Honey-Pi/honeypi-pcb/PCB_V2.x/Schaltplan-27-9-2020.pdf

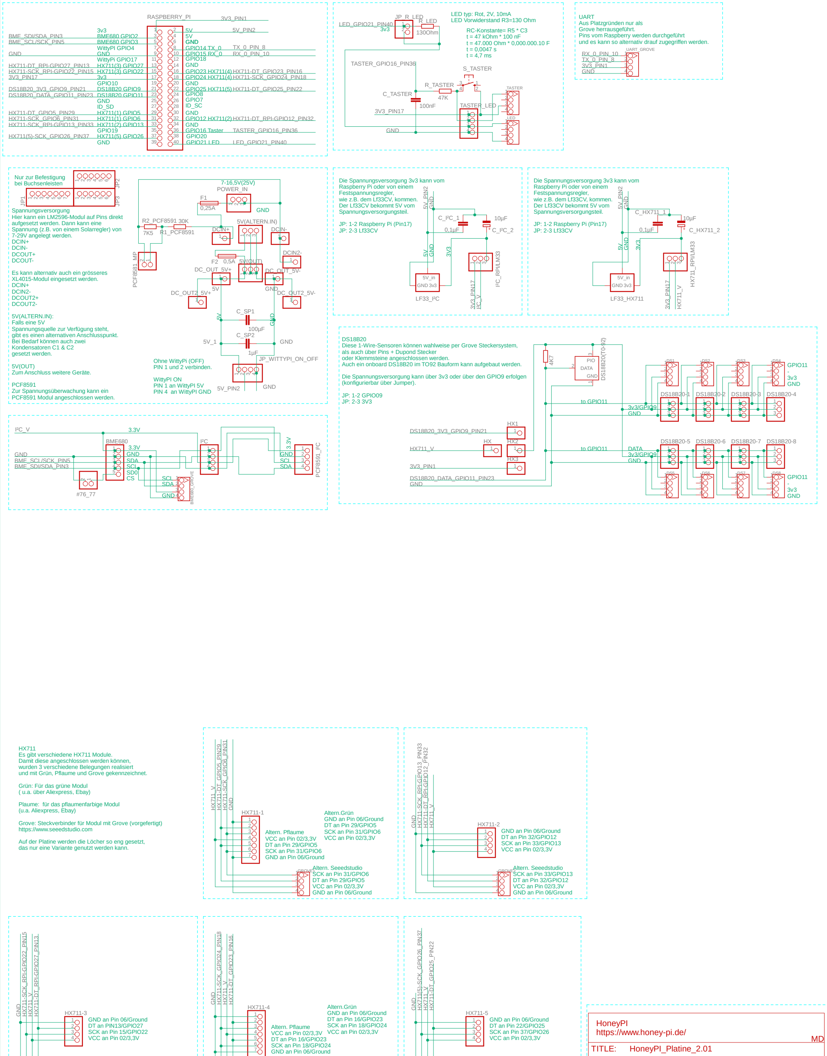
[picture p17: figure]
130Ohm; GND; RASPBERRY_PI; 4 TASTER_LED; R_LED; 1 DCIN+; 1 DCIN- 1 DC_OUT_5V+; 1 DC_OUT_5V- ¹; 3 POWER_IN; PIO; DATA 2; DS¹⁸B²⁰⁽T0⁻92⁾; 5V(OUT); R2_PCF8591; R1_PCF8591; LED; 4TASTER; C_TASTER; R_TASTER; 4GROVE1; 4GROVE2; SDA; 4 BME⁶⁸⁰_GROVE; 4UART_GROVE; 4 PCF8591_I²C; 3 I²C_RPI/LM33; C_I²C_1; 1 DC_OUT2_5V+; 1 DCIN2- 1 DC_OUT2_5V-; 4 2 S_TASTER; 1 PCF8581_MP; I²C; 5 BME680; 3 HX711_RPI/LM33; JP_WITTYPI_ON_OFF; 5V(ALTERN.IN); 5V_in GND 3v3; LF33_I²C; C_I²C_2; JP_R_LED; BME_SCL/SCK_PIN5; HX⁷¹¹_V; HX⁷¹¹_V HX⁷¹¹_V; DS18B20_3V3_GPIO9_PIN21; LED_GPIO21_PIN40; TASTER_GPIO16_PIN36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

1
2
3

4GROVE3

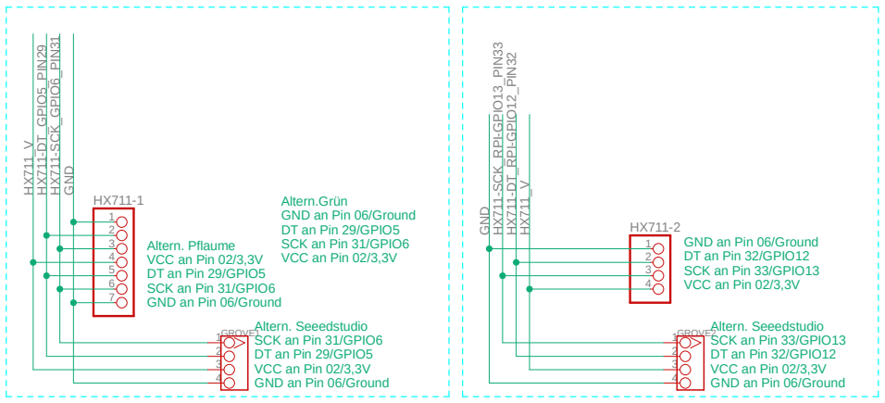
[picture p18: figure]

1
2
3
4GROVE4 | 1
2
3

4GROVE5

HX711-DT_GPIO5_PIN29 | HX⁷¹¹⁻DT_GPIO⁵_PIN²⁹
HX711-DT_RPI-GPIO12_PIN32 | HX⁷¹¹⁻DT_RPI-GPIO¹²_PIN³²

# TASTER_GPIO16_PIN36 HX⁷¹¹⁻SCK_RPI-GPIO¹³_PIN³³

HX711-DT_RPI-GPIO27_PIN13 HX⁷¹¹⁻SCK_RPI-GPIO²²_PIN¹⁵ | HX⁷¹¹⁻DT_RPI-GPIO²⁷_PIN¹³
HX711-SCK_RPI-GPIO22_PIN15 | HX711-DT_GPIO23_PIN16 HX⁷¹¹⁻DT_GPIO²³_PIN¹⁶

# HX711-SCK_GPIO24_PIN18 HX⁷¹¹⁻SCK_GPIO²⁴_PIN¹⁸

HX711-SCK_GPIO6_PIN31 | HX⁷¹¹⁻SCK_GPIO⁶_PIN³¹
HX711-DT_GPIO25_PIN22 | HX⁷¹¹⁽⁵⁾⁻SCK_GPIO²⁶_PIN³⁷ | HX⁷¹¹⁻DT_GPIO²⁵_PIN²²
Date: | Sheet:

## REV:

## Document Number:

27.09.2020 13:27 | 1/1

Altern. Pflaume VCC an Pin 02/3,3V DT an Pin 29/GPIO5 SCK an Pin 31/GPIO6 GND an Pin 06/Ground

Altern.Grün GND an Pin 06/Ground DT an Pin 29/GPIO5 SCK an Pin 31/GPIO6 VCC an Pin 02/3,3V

DS18B20 GPIO9 DS18B20 GPIO11 HX711(1) GPIO5

HX711(2) GPIO13 GND GND | GND GPIO16 Taster GPIO21 LED GND GND GND GND
Altern. Seeedstudio SCK an Pin 31/GPIO6 DT an Pin 29/GPIO5 VCC an Pin 02/3,3V GND an Pin 06/Ground | GND an Pin 06/Ground DT an Pin 32/GPIO12 SCK an Pin 33/GPIO13 VCC an Pin 02/3,3V

Altern. Seeedstudio SCK an Pin 33/GPIO13 DT an Pin 32/GPIO12 VCC an Pin 02/3,3V GND an Pin 06/Ground GND an Pin 06/Ground DT an PIN13/GPIO27 SCK an Pin 15/GPIO22 VCC an Pin 02/3,3V

Altern. Seeedstudio SCK an Pin 15/GPIO22 DT an PIN13/GPIO27 VCC an Pin 02/3,3V GND an Pin 06/Ground | Altern. Pflaume VCC an Pin 02/3,3V DT an Pin 16/GPIO23 SCK an Pin 18/GPIO24 GND an Pin 06/GroundAltern.Grün GND an Pin 06/Ground DT an Pin 16/GPIO23 SCK an Pin 18/GPIO24 VCC an Pin 02/3,3V
Altern. Seeedstudio SCK an Pin 18/GPIO24 DT an Pin 16/GPIO23 VCC an Pin 02/3,3V GND an Pin 06/Ground | GND an Pin 06/Ground DT an Pin 22/GPIO25 SCK an Pin 37/GPIO26 VCC an Pin 02/3,3V

Altern. Seeedstudio SCK an Pin 37/GPIO26 DT an Pin 22/GPIO25 VCC an Pin 02/3,3V GND an Pin 06/Ground

HX711 Es gibt verschiedene HX711 Module.

und mit Grün, Pflaume und Grove gekennzeichnet.

Grove: Steckverbinder für Modul mit Grove (vorgefertigt)

Auf der Platine werden die Löcher so eng gesetzt,
das nur eine Variante genutzt werden kann.

DS18B20 Diese 1-Wire-Sensoren können wahlweise per Grove Steckersystem,

Auch ein onboard DS18B20 im TO92 Bauform kann aufgebaut werden.

Die Spannungsversorgung kann über 3v3 oder über den GPIO9 erfolgen (konfigurierbar über Jumper). JP: 1-2 GPIO09

und es kann so alternativ drauf zugegriffen werden.

Spannungsversorgung Hier kann ein LM2596-Modul auf Pins direkt aufgesetzt werden. Dann kann eine

Spannung (z.B. von einem Solarregler) von 7-29V angelegt werden. DCIN+ DCIN- DCOUT+ DCOUT- Es kann alternativ auch ein grösseres

XL4015-Modul eingesetzt werden. DCIN+ DCIN2- DCOUT2+ DCOUT2- 5V(ALTERN.IN): Falls eine 5V

gibt es einen alternativen Anschlusspunkt. Bei Bedarf können auch zwei Kondensatoren C1 & C2

5V(OUT) Zum Anschluss weitere Geräte. PCF8591 Zur Spannungsüberwachung kann ein

wie z.B. dem Lf33CV, kommen. Der Lf33CV bekommt 5V vom

JP: 1-2 Raspberry Pi (Pin17) JP: 2-3 Lf33CV wie z.B. dem Lf33CV, kommen. Der Lf33CV bekommt 5V vom

JP: 1-2 Raspberry Pi (Pin17) JP: 2-3 Lf33CV

A

B

C

D

E

1 | 2 | 3 | 4 | 5 | 6 | 7 | 8

A

B

C

D

E

1 | 2 | 3 | 4 | 5 | 6 | 7 | 8

Ohne WittyPi (OFF) PIN 1 und 2 verbinden. WittyPI ON
