Honey-Pi/honeypi-pcb/PCB_V2.x/Schaltplan-21-8-2020.pdf

100µF

1µF

130Ohm

130Ohm | 4K⁷
5V | GND

7K5

30K

100nF

47K

0,1µF | 0,1µF
10µF | 10µF

0,25A

0,5A

1 2
3 4
5 6
7 8
9 10
11 12
13 14
15 16
17 18
19 20
21 22
23 24
25 26
27 28
29 30
31 32
33 34
35 36
37 38
39 40

RASPBERRY_PI

C_SP1

C_SP2

1
2
3

### 4 TASTER_LED

R_LED

### 1 DCIN+

### 1 DCIN- 1 DC_OUT_5V+

### 1 DC_OUT_5V- ¹

2

### 3 POWER_IN

1
2
3
4
5
6

# 7 HX711-1

PIO

GND

DATA 2 | 1 3 | DS¹⁸B²⁰⁽T0⁻92⁾

1

2

3

5V(OUT)

1
2

### 3 DS18B20-8

1
2

### 3 DS18B20-4

1
2

### 3 DS18B20-3

1
2

### 3 DS18B20-2

1
2

### 3 DS18B20-1

1
2

### 3 DS18B20-6

1
2

### 3 DS18B20-7

1
2

### 3 DS18B20-5

R2_PCF8591

R1_PCF8591

1
2
3

4DS8 1
2
3

4DS7 1
2
3

4DS6 1
2
3

4DS5

1
2
3
4DS1 | 1
2
3
4DS2 | 1
2
3
4DS3 | 1
2
3

4DS4

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
4TASTER

1
2
3

JP_VORW

C_TASTER

R_TASTER

1
2
3
4SEEED1 | 1
2
3

4SEEED2

1
2
3

4SEEED3

1
2
3
4
5
6

# 7 HX711-4

1
2
3
4SEEED4 | 1
2
3

4SEEED5

1
2
3

### 4 BME⁶⁸⁰_GROVE

1
2
3

4UART_GROVE

1
2
3

### 4 PCF8591_I²C

1

2

### 3 I²C_RPI/LM33

C_I²C_1

### 1 DC_OUT2_5V+

### 1 DCIN2- 1 DC_OUT2_5V-

3 1

4 2 S_TASTER

2

### 1 PCF8581_MP

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
### 5 BME680

1
2
3

### 4 HX711-3

1
2
3

### 4 HX711-2

1
2
3

### 4 HX711-5

1

2

# 3 HX711_RPI/LM33

C_HX711_1

1

2

3

4

JP_WITTYPI_ON_OFF

1

2

3

5V(ALTERN.IN)

### 1 HX

2

1

#76_77

5V_in GND 3v3

LM33_I²C

5V_in GND 3v3

LM33_HX711

C_I²C_2 | C_HX711_2 F1 F2
1

2

3

4

5

6

### 7 JP1

1

2

3

4

5

### 6 JP2

1

2

3

4

5

### 6 JP3

### 1 HX1

### 1 HX2

### 1 HX3

# HX711-DT_GPIO5_PIN29 HX⁷¹¹⁻DT_GPIO⁵_PIN²⁹

BME_SCL/SCK_PIN5

BME_SCL/SCK_PIN5 | HX⁷¹¹_V | HX⁷¹¹_V | HX⁷¹¹_V HX⁷¹¹_V | HX⁷¹¹_V | HX⁷¹¹_V

HX711_V

# HX711-DT_RPI-GPIO12_PIN32 HX⁷¹¹⁻DT_RPI-GPIO¹²_PIN³²

DS18B20_3V3_GPIO9_PIN21

DS18B20_3V3_GPIO9_PIN21

LED_GPIO21_PIN40

LED_GPIO21_PIN40

TASTER_GPIO16_PIN36

# TASTER_GPIO16_PIN36 HX⁷¹¹⁻SCK_RPI-GPIO¹³_PIN³³

HX711-SCK_RPI-GPIO13_PIN33

HX711-DT_RPI-GPIO27_PIN13 HX⁷¹¹⁻SCK_RPI-GPIO²²_PIN¹⁵ | HX⁷¹¹⁻DT_RPI-GPIO²⁷_PIN¹³
HX711-SCK_RPI-GPIO22_PIN15 | HX711-DT_GPIO23_PIN16 HX⁷¹¹⁻DT_GPIO²³_PIN¹⁶

# HX711-SCK_GPIO24_PIN18 HX⁷¹¹⁻SCK_GPIO²⁴_PIN¹⁸

HX711-SCK_GPIO6_PIN31 | HX⁷¹¹⁻SCK_GPIO⁶_PIN³¹
HX711-DT_GPIO25_PIN22 | HX⁷¹¹⁽⁵⁾⁻SCK_GPIO²⁶_PIN³⁷ | HX⁷¹¹⁻DT_GPIO²⁵_PIN²²

HX711(5)-SCK_GPIO26_PIN37

TX_0_PIN_8

TX_0_PIN_8

RX_0_PIN_10

RX_0_PIN_10

BME_SDI/SDA_PIN3

BME_SDI/SDA_PIN3

3V3_PIN17

3V3_PIN17 | 3V³_PIN¹⁷ | 3V³_PIN¹⁷

3V3_PIN1

3V3_PIN1

3V3_PIN1

I²C_V | I²C_V ⁵V_PIN²
5V_PIN2 | 5V_PIN²

5V_PIN2

DS18B20_DATA_GPIO11_PIN23

DS18B20_DATA_GPIO11_PIN23

5V_1 | GND GND

GND

GND GND

GND | GND GND | GND GND | GND GND | GND | GND

## HoneyPI

https://www.honey-pi.de/ | MD
Date: | Sheet:

## REV:

## TITLE:

## Document Number:

21.08.2020 11:47 | 1/1

## HoneyPI_Platine_2.01

+

+

3v3

5V

3v3/GPIO9 GND | DATA
SCL | GND

SDA

SD0 CS

3v3 5V | GND GND

7-16,5V(25V)

Altern. Pflaume VCC an Pin 02/3,3V DT an Pin 29/GPIO5 SCK an Pin 31/GPIO6 GND an Pin 06/Ground

GPIO18

Altern.Grün GND an Pin 06/Ground DT an Pin 29/GPIO5 SCK an Pin 31/GPIO6 VCC an Pin 02/3,3V

BME680 GPIO2 BME680 GPIO3 WittyPI GPIO4

WittyPi GPIO17 GND

DS18B20 GPIO9 DS18B20 GPIO11 HX711(1) GPIO5

HX711(1) GPIO6

HX711(2) GPIO13 GND GND | GND GPIO16 Taster GPIO21 LED GND GND GND GND 5VGPIO12 HX711(2)

3v3/GPIO9 GND

to GPIO11 | GPIO11

-3v3 GND

GPIO11
-3v3 GND

to GPIO11

GPIO23 HX711(4)
GPIO24 HX711(4)

GPIO25 HX711(5)

HX711(5) GPIO26 | GND GPIO15 RX_0 GPIO14 TX_0

HX711(3) GPIO27
HX711(3) GPIO22
Altern. Seeedstudio SCK an Pin 31/GPIO6 DT an Pin 29/GPIO5 VCC an Pin 02/3,3V GND an Pin 06/Ground | GND an Pin 06/Ground DT an Pin 32/GPIO12 SCK an Pin 33/GPIO13 VCC an Pin 02/3,3V

Altern. Seeedstudio SCK an Pin 33/GPIO13 DT an Pin 32/GPIO12 VCC an Pin 02/3,3V GND an Pin 06/Ground GND an Pin 06/Ground DT an PIN13/GPIO27 SCK an Pin 15/GPIO22 VCC an Pin 02/3,3V

Altern. Seeedstudio SCK an Pin 15/GPIO22 DT an PIN13/GPIO27 VCC an Pin 02/3,3V GND an Pin 06/Ground | Altern. Pflaume VCC an Pin 02/3,3V DT an Pin 16/GPIO23 SCK an Pin 18/GPIO24 GND an Pin 06/GroundAltern.Grün GND an Pin 06/Ground DT an Pin 16/GPIO23 SCK an Pin 18/GPIO24 VCC an Pin 02/3,3V
Altern. Seeedstudio SCK an Pin 18/GPIO24 DT an Pin 16/GPIO23 VCC an Pin 02/3,3V GND an Pin 06/Ground | GND an Pin 06/Ground DT an Pin 22/GPIO25 SCK an Pin 37/GPIO26 VCC an Pin 02/3,3V

Altern. Seeedstudio SCK an Pin 37/GPIO26 DT an Pin 22/GPIO25 VCC an Pin 02/3,3V GND an Pin 06/Ground

GND

SDA

# SCL³.3V GPIO8 GPIO7

ID_SC GPIO20

# ID_SD GPIO10 GPIO19

HX711 Es gibt verschiedene HX711 Module.

Damit diese angeschlossen werden können, wurden 3 verschiedene Belegungen realisiert
und mit Grün, Pflaume und SEEED gekennzeichnet.

Grün: Für das grüne Modul
( u.a. über Aliexpress, Ebay)

Plaume: für das pflaumenfarbige Modul
(u.a. Aliexpress, Ebay)

Seeed: Modul mit Grove vorgefertigt https://www.seeedstudio.com

Auf der Platine werden die Löcher so eng gesetzt, das nur eine Variante genutzt werden kann.

DS18B20 Diese 1-Wire-Sensoren können wahlweise per Grove Steckersystem,

als auch über Pins + Dupond Stecker
oder Klemmsteine angeschlossen werden.
Auch ein onboard DS18B20 im TO92 Bauform kann aufgebaut werden.

Die Spannungsversorgung kann über 3v3 oder über den GPIO9 erfolgen (konfigurierbar über Jumper). JP: 1-2 GPIO09

JP: 2-3 3V3

UART Aus Platzgründen nur als

Grove herrausgeführt.
Pins vom Raspberry werden durchgeführt
und es kann so alternativ drauf zugegriffen werden.

Spannungsversorgung Hier kann ein LM2596-Modul auf Pins direkt aufgesetzt werden. Dann kann eine

Spannung (z.B. von einem Solarregler) von 7-29V angelegt werden. DCIN+ DCIN- DCOUT+ DCOUT- Es kann alternativ auch ein grösseres

XL4015-Modul eingesetzt werden. DCIN+ DCIN2- DCOUT2+ DCOUT2- 5V(ALTERN.IN): Falls eine 5V

Spannungsquelle zur Verfügung steht, gibt es einen alternativen Anschlusspunkt. Bei Bedarf können auch zwei Kondensatoren C1 & C2

gesetzt werden.

5V(OUT) Zum Anschluss weitere Geräte. PCF8591 Zur Spannungsüberwachung kann ein

PCF8591 Modul angeschlossen werden. | 5VGND | 3V³
3v3 | Die Spannungsversorgung 3v3 kann vom

Raspberry Pi oder von einem Festspannungsregler,
wie z.B. dem LM33CV, kommen. Der LM33CV bekommt 5V vom

Spannungsversorgungsteil.

JP: 1-2 Raspberry Pi (Pin17) JP: 2-3 LM33CV

RC-Konstante= R5 * C3
t = 47 kOhm * 100 nF
t = 47.000 Ohm * 0,000.000.10 F t = 0,0047 s
t = 4,7 ms

LED typ: Rot, 2V, 10mA
LED Vorwiderstand R3=130 Ohm

3.3V

3.3V | GND

SDA

SCL | 5VGND | 3V³

Die Spannungsversorgung 3v3 kann vom Raspberry Pi oder von einem Festspannungsregler,
wie z.B. dem LM33CV, kommen. Der LM33CV bekommt 5V vom

Spannungsversorgungsteil.

JP: 1-2 Raspberry Pi (Pin17) JP: 2-3 LM33CV

A

B

C

D

E

1 | 2 | 3 | 4 | 5 | 6 | 7 | 8

A

B

C

D

E

1 | 2 | 3 | 4 | 5 | 6 | 7 | 8

Ohne WittyPi (OFF) PIN 1 und 2 verbinden. WittyPI ON

PIN 1 an WittyPI 5V
PIN 4 an WittyPI GND

Nur zur Befestigung
bei Buchsenleisten
