Honey-Pi/honeypi-pcb/PCB_Sensor_Board_2.x_BME280_680_ATH10_HDC1080/Datasheets/Gehäusemaße.jpg

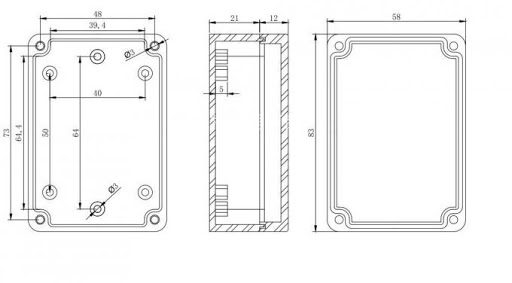
PCB_Sensor_Board_2.x_BME280_680_ATH10_HDC1080/Datasheets/Gehäusemaße.jpg
