Honey-Pi/honeypi-pcb/PCB_V3.x/Doku/D1.png

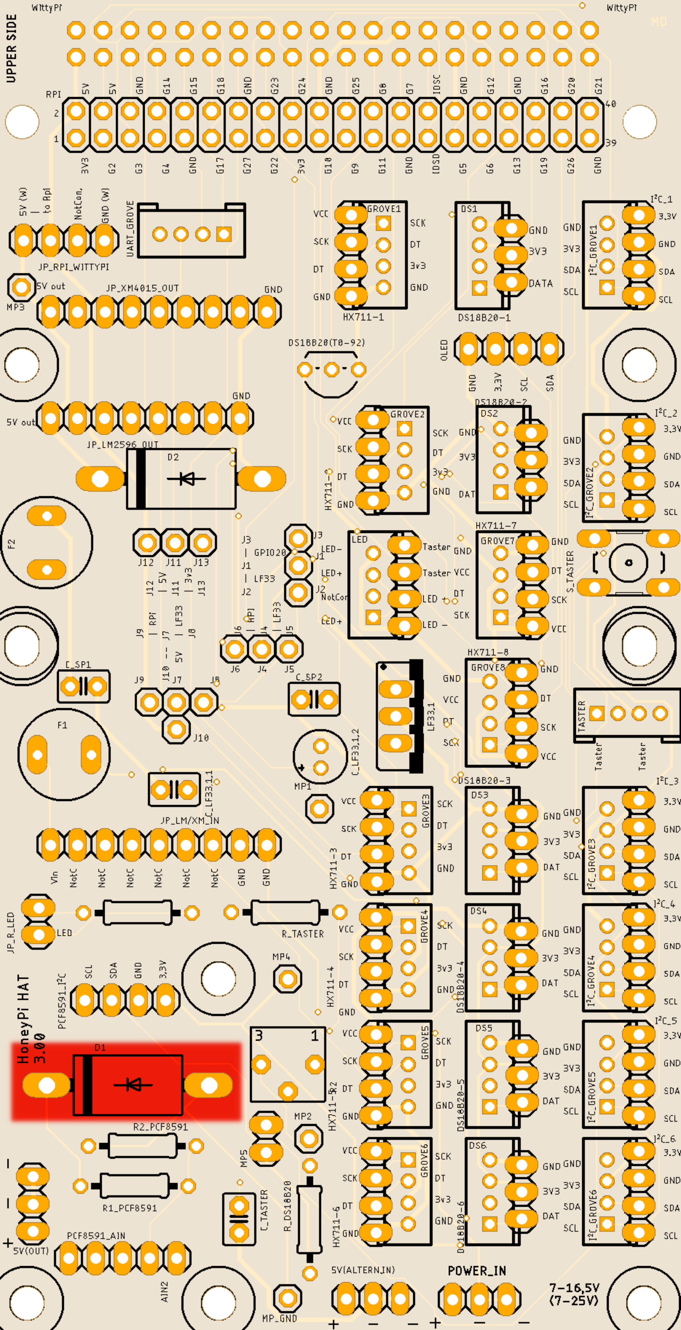
PCB_V3.x/Doku/D1.png
