Honey-Pi/honeypi-pcb/PCB_V3.x/Doku/D2.png

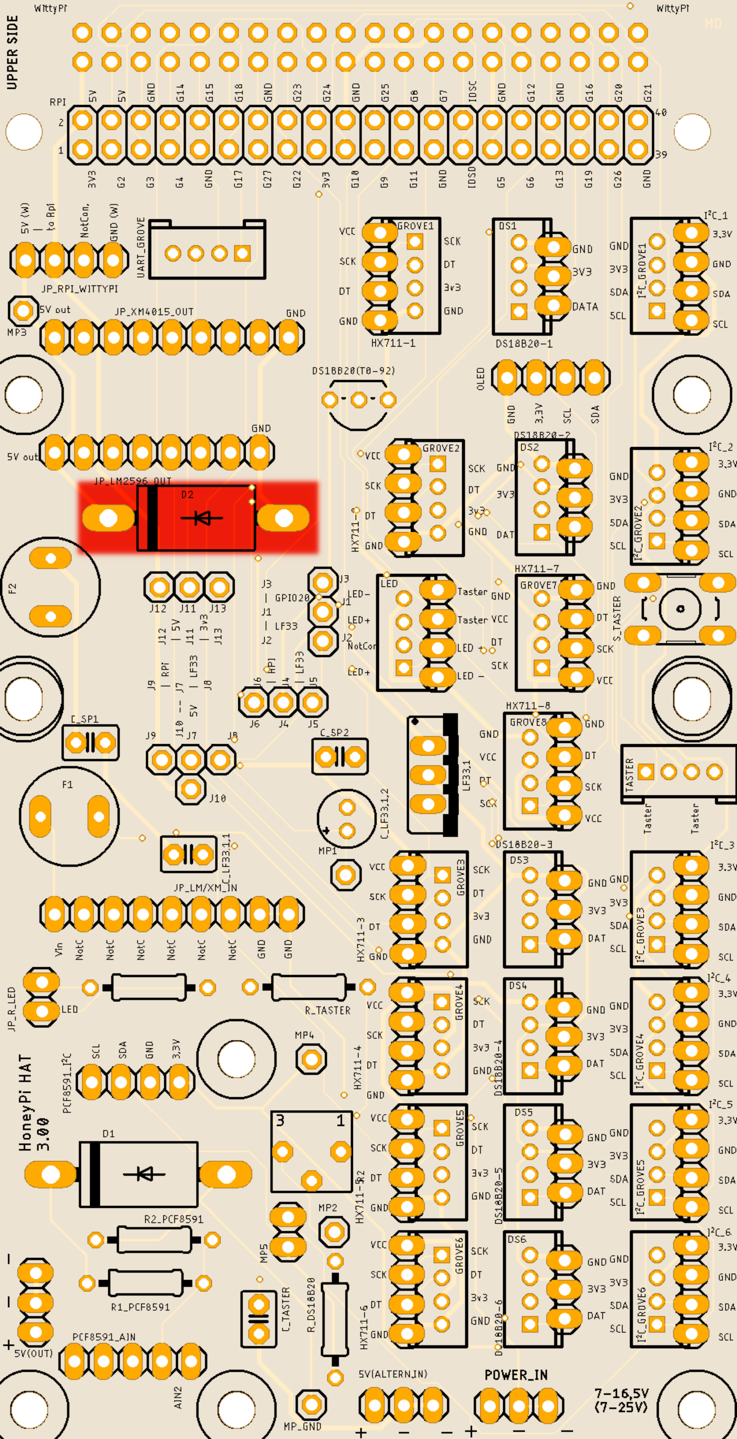
PCB_V3.x/Doku/D2.png
