Honey-Pi/honeypi-pcb/PCB_V3.x/Doku/ds18b20.png

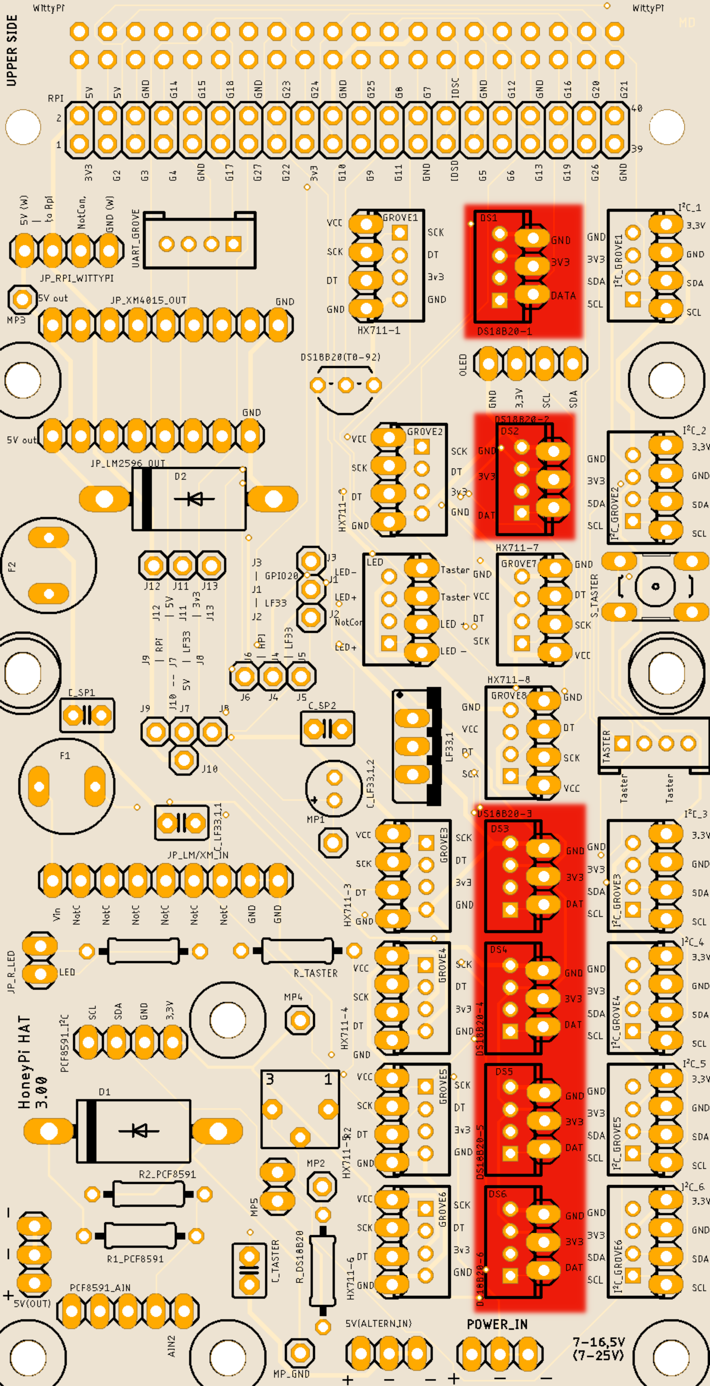
PCB_V3.x/Doku/ds18b20.png
