Honey-Pi/honeypi-pcb/PCB_V3.x/Doku/DS18B20_kompl.png

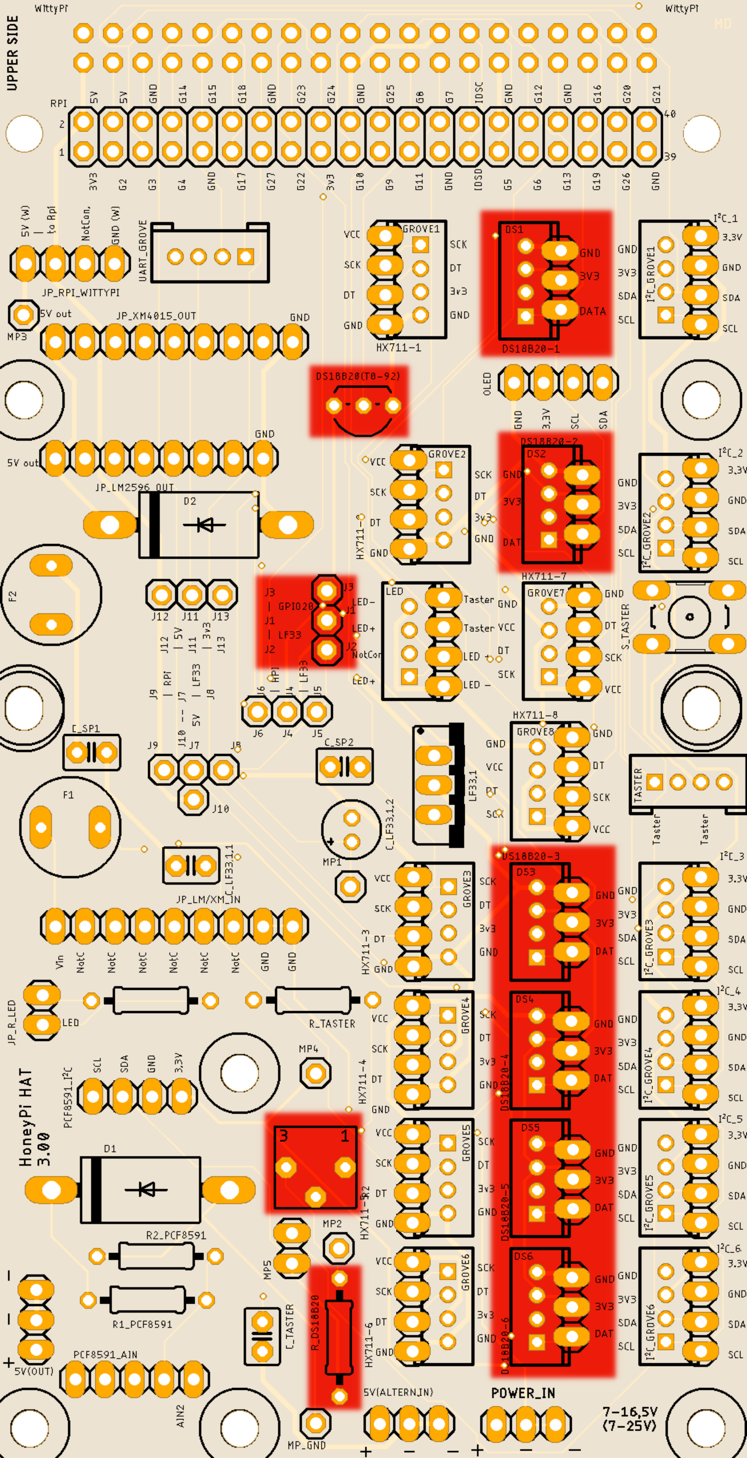
PCB_V3.x/Doku/DS18B20_kompl.png
