Honey-Pi/honeypi-pcb/PCB_V3.x/Doku/DS18B20_Potent_R.png

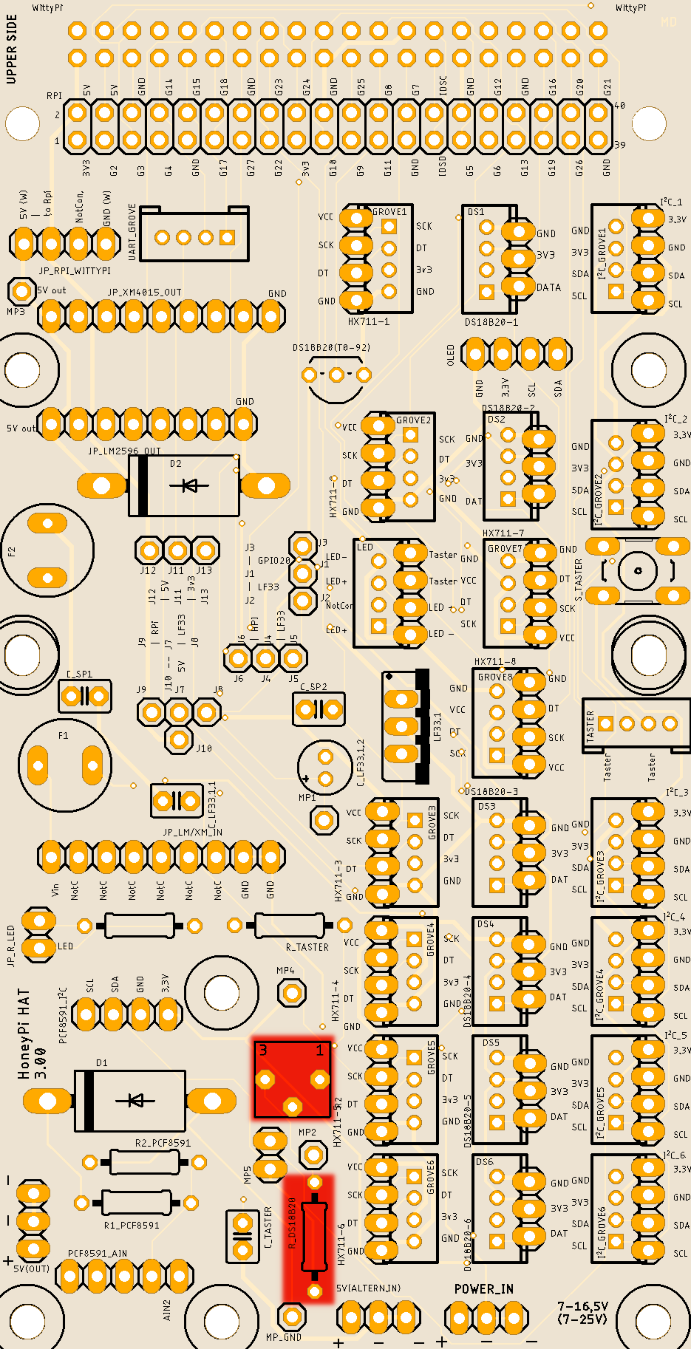
PCB_V3.x/Doku/DS18B20_Potent_R.png
