Honey-Pi/honeypi-pcb/PCB_V3.x/Doku/Ds18B20OnBoard.png

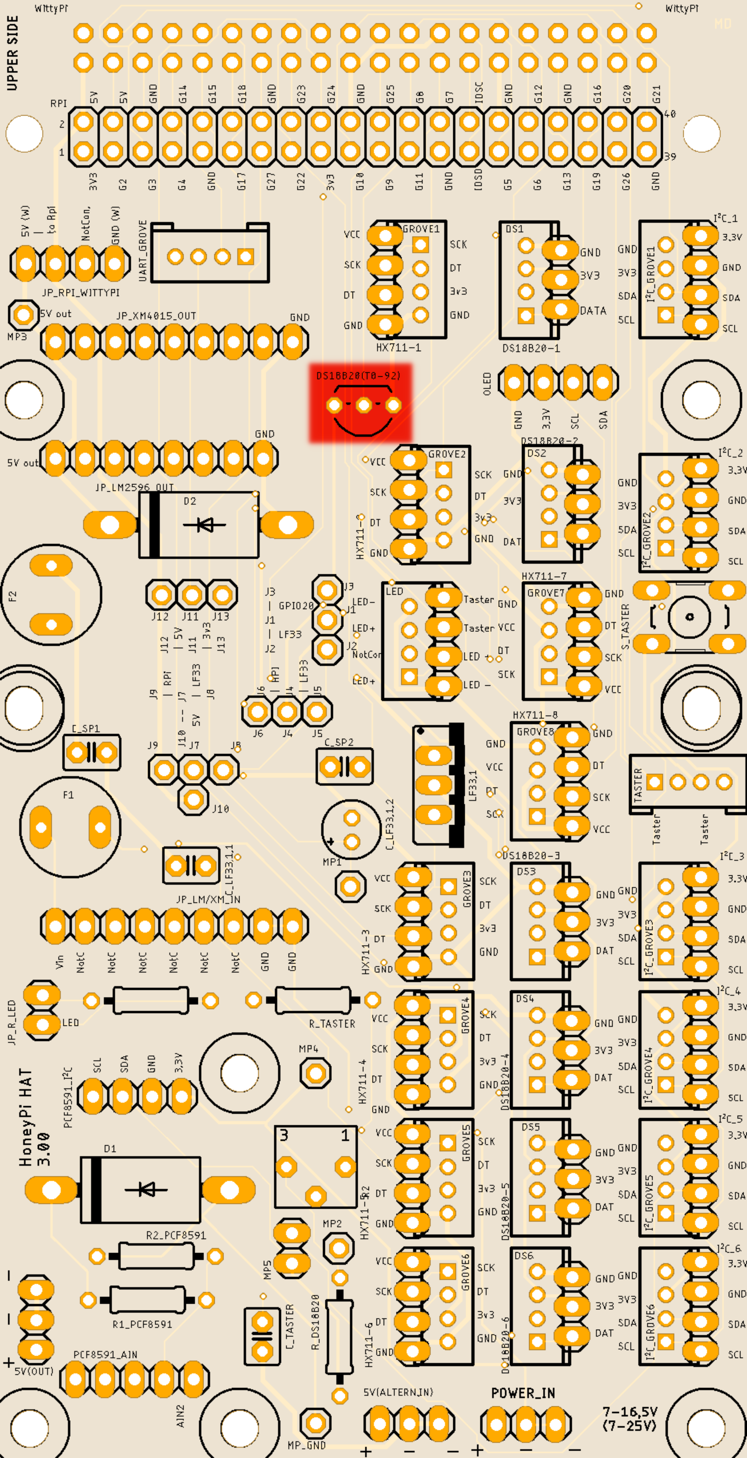
PCB_V3.x/Doku/Ds18B20OnBoard.png
