Honey-Pi/honeypi-pcb/PCB_V3.x/Doku/F1.png

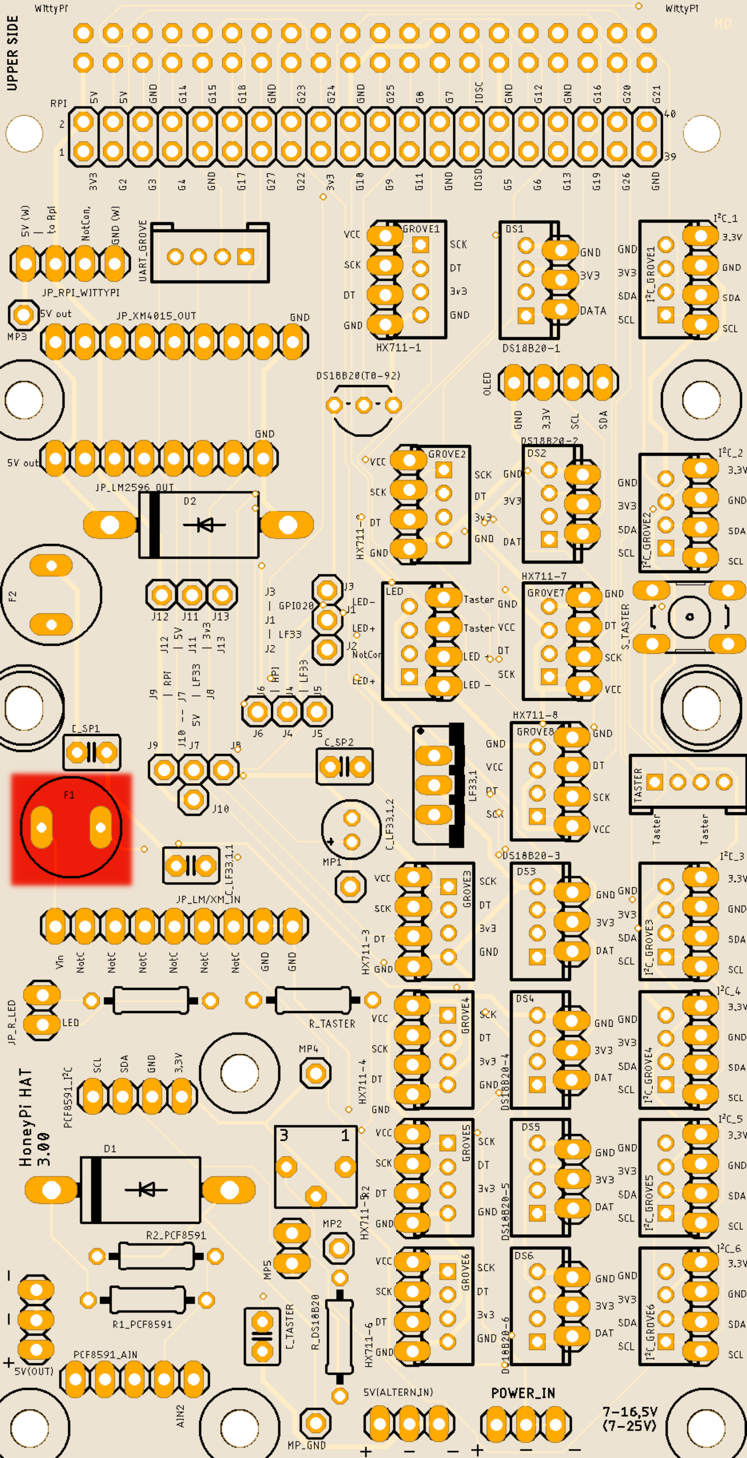
PCB_V3.x/Doku/F1.png
