Honey-Pi/honeypi-pcb/PCB_V3.x/Doku/hx711.png

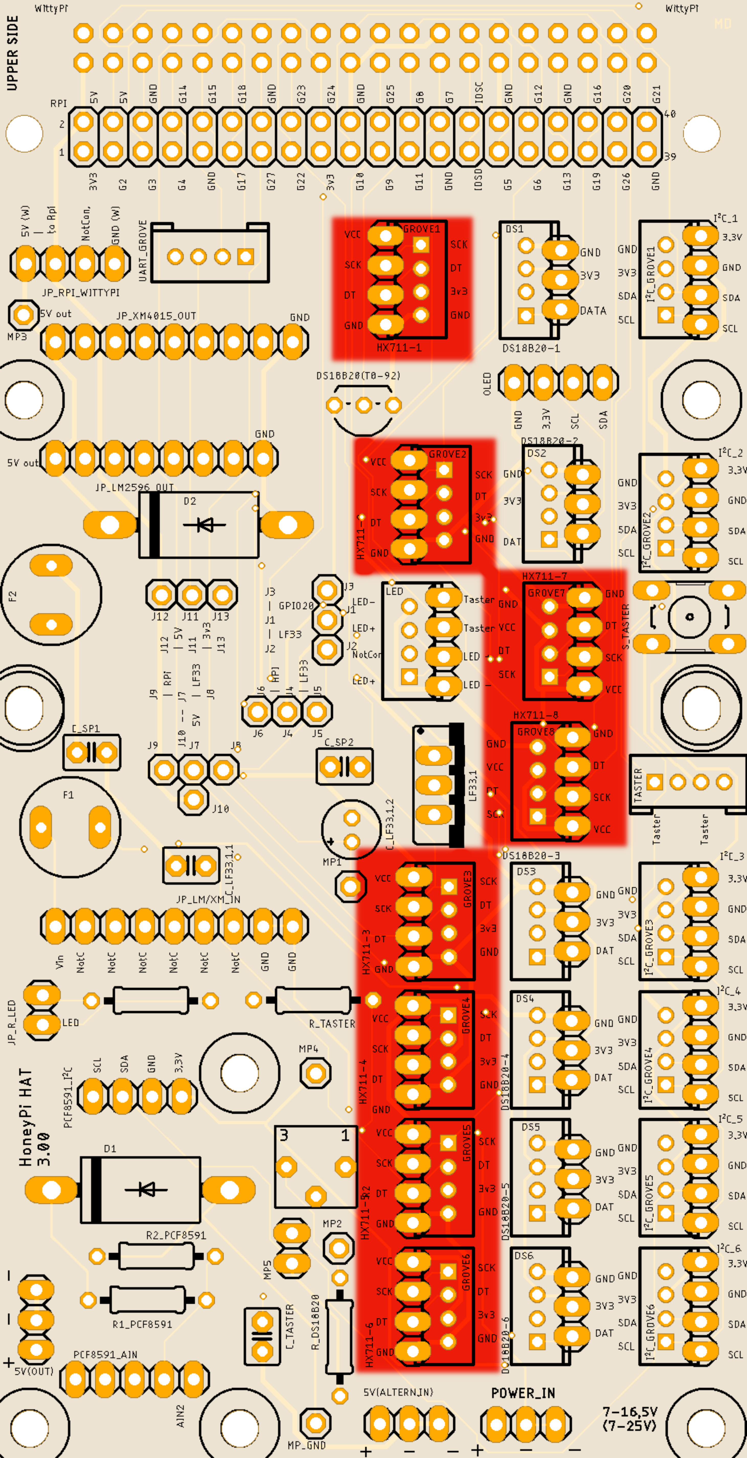
PCB_V3.x/Doku/hx711.png
