Honey-Pi/honeypi-pcb/PCB_V3.x/Doku/I2c.png

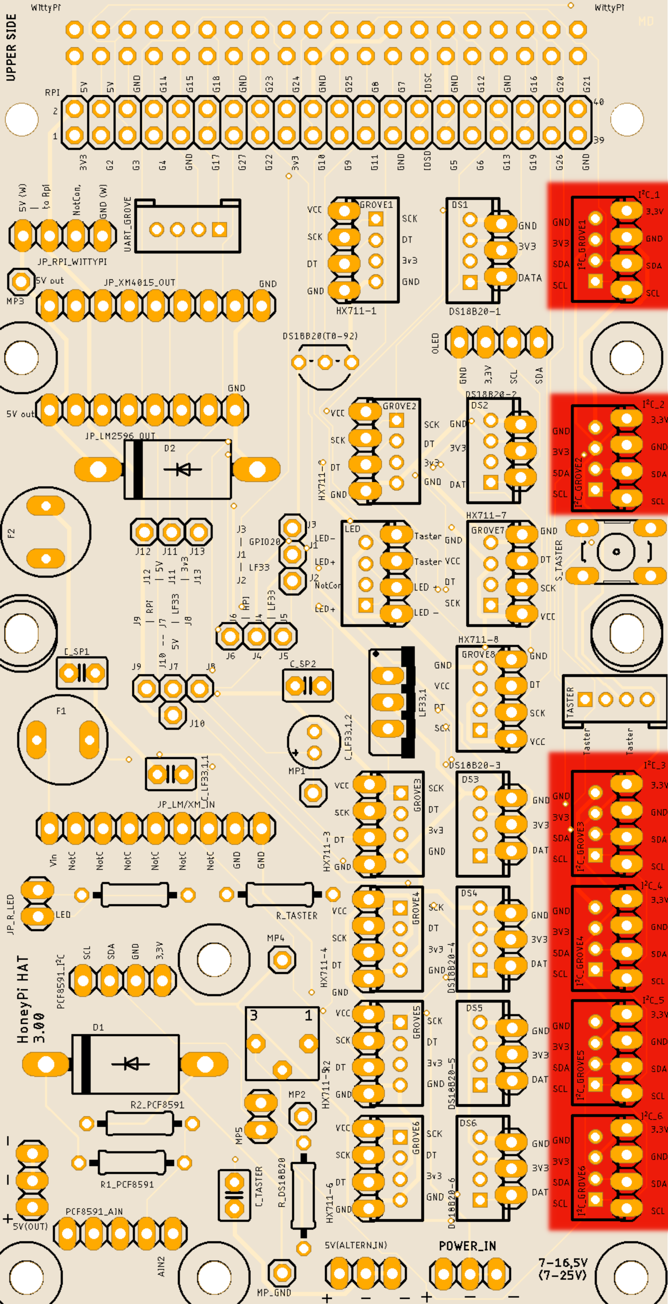
PCB_V3.x/Doku/I2c.png
