Honey-Pi/honeypi-pcb/PCB_V3.x/Doku/LF33.png

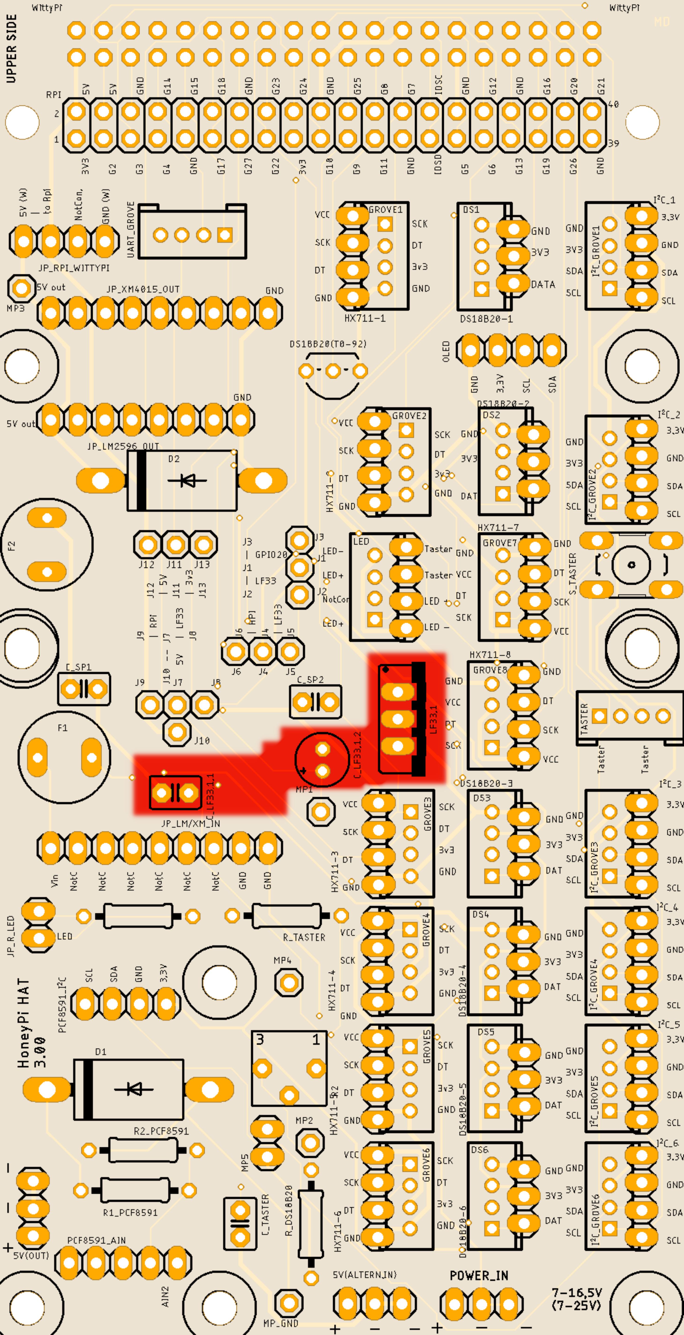
PCB_V3.x/Doku/LF33.png
