Honey-Pi/honeypi-pcb/PCB_V3.x/Doku/LM2596.png

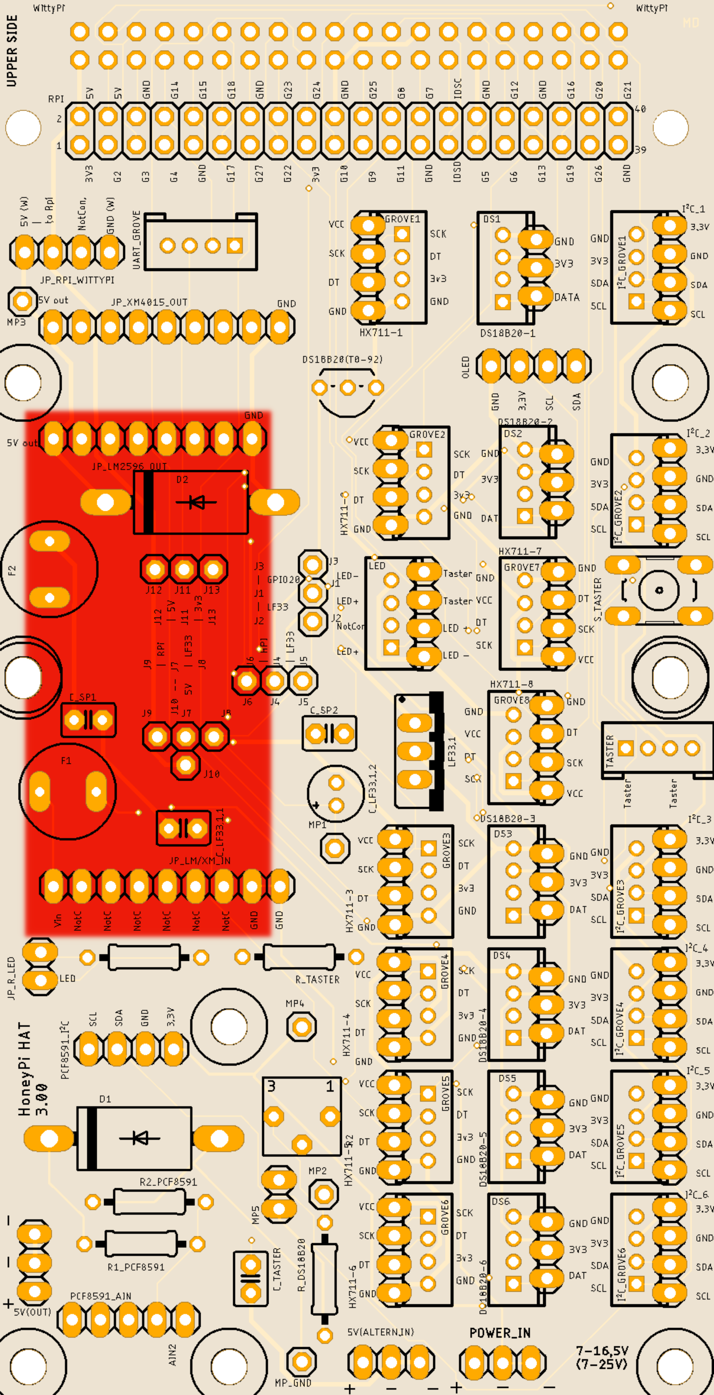
PCB_V3.x/Doku/LM2596.png
