Honey-Pi/honeypi-pcb/PCB_V3.x/Doku/pcf.png

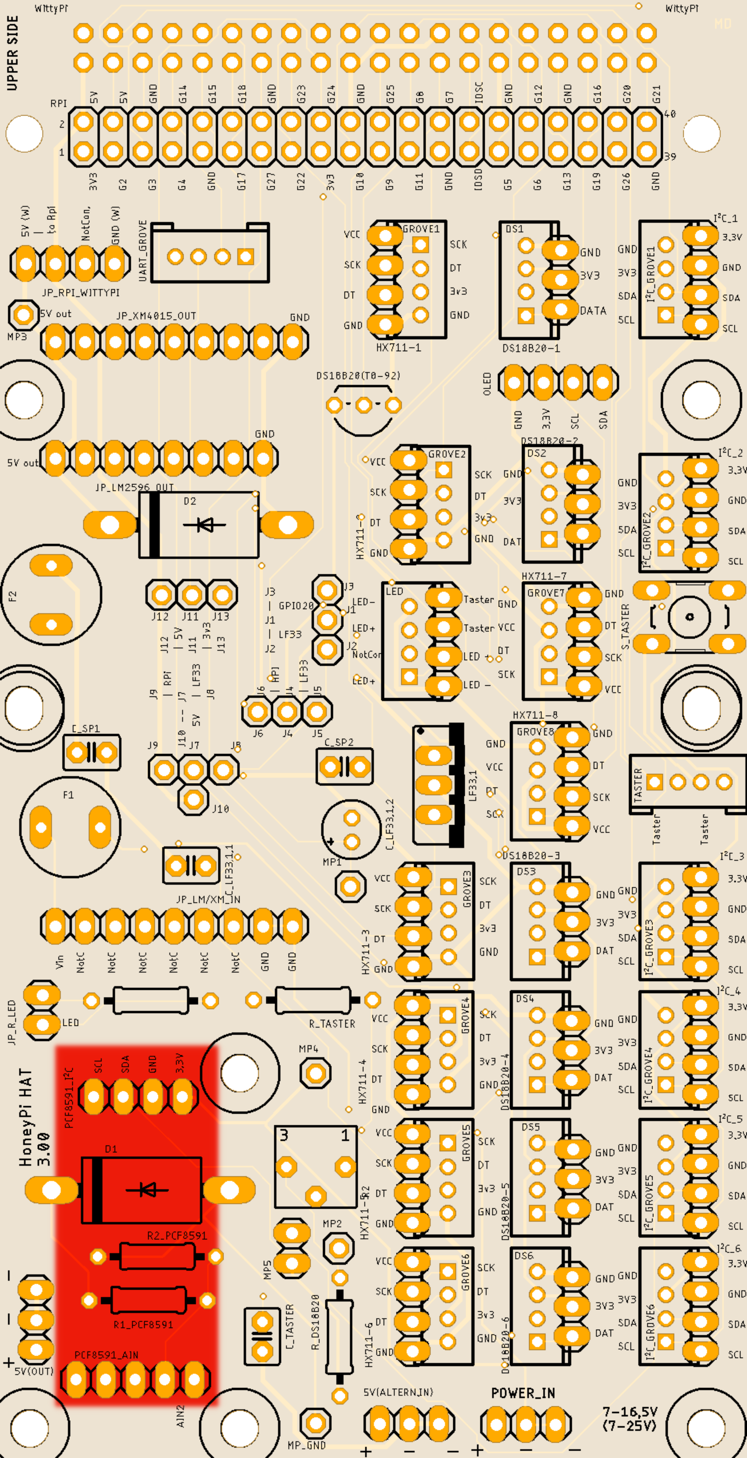
PCB_V3.x/Doku/pcf.png
