Honey-Pi/honeypi-pcb/PCB_V3.x/Doku/Power_Alternativ_ohne WittyPi_kompl.png

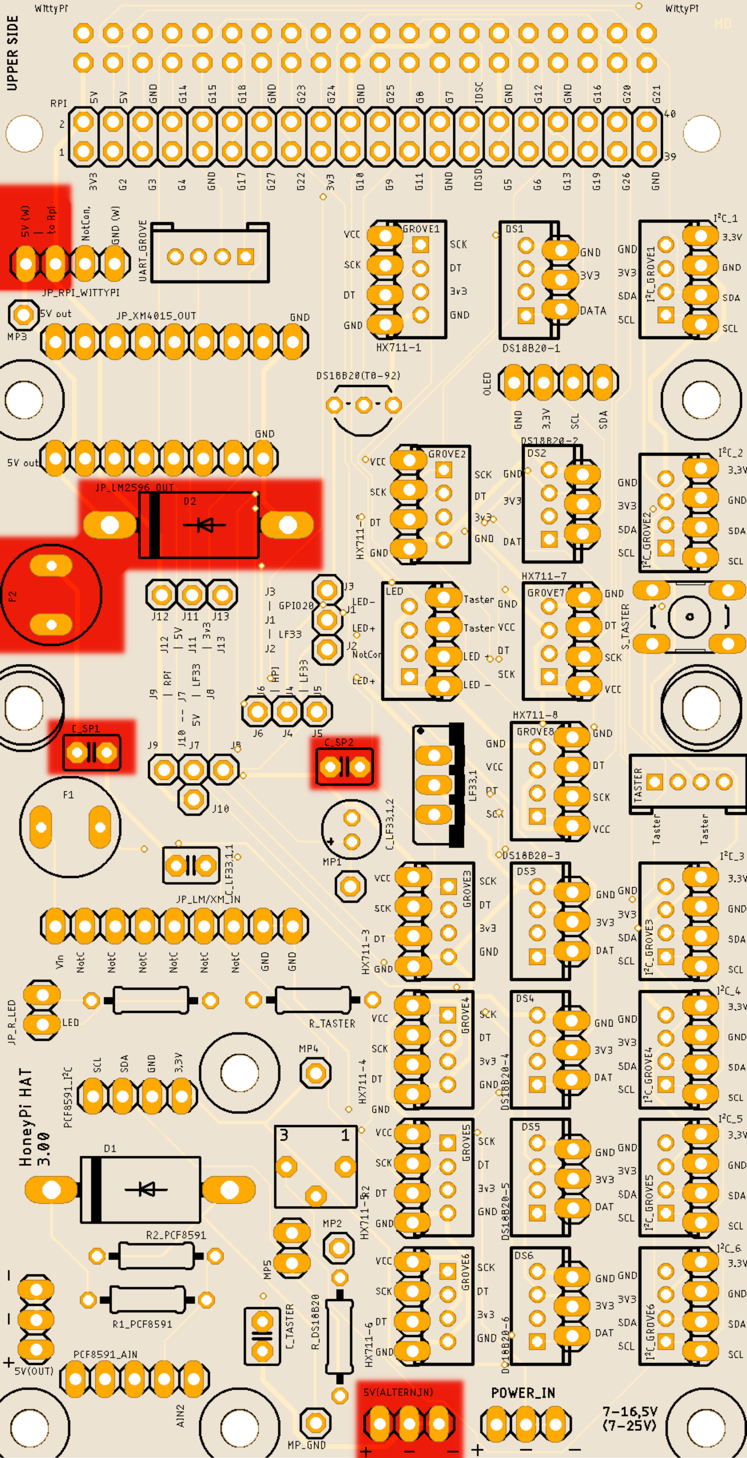
PCB_V3.x/Doku/Power_Alternativ_ohne WittyPi_kompl.png
