Honey-Pi/honeypi-pcb/PCB_V3.x/Doku/PowerAlternativ.png

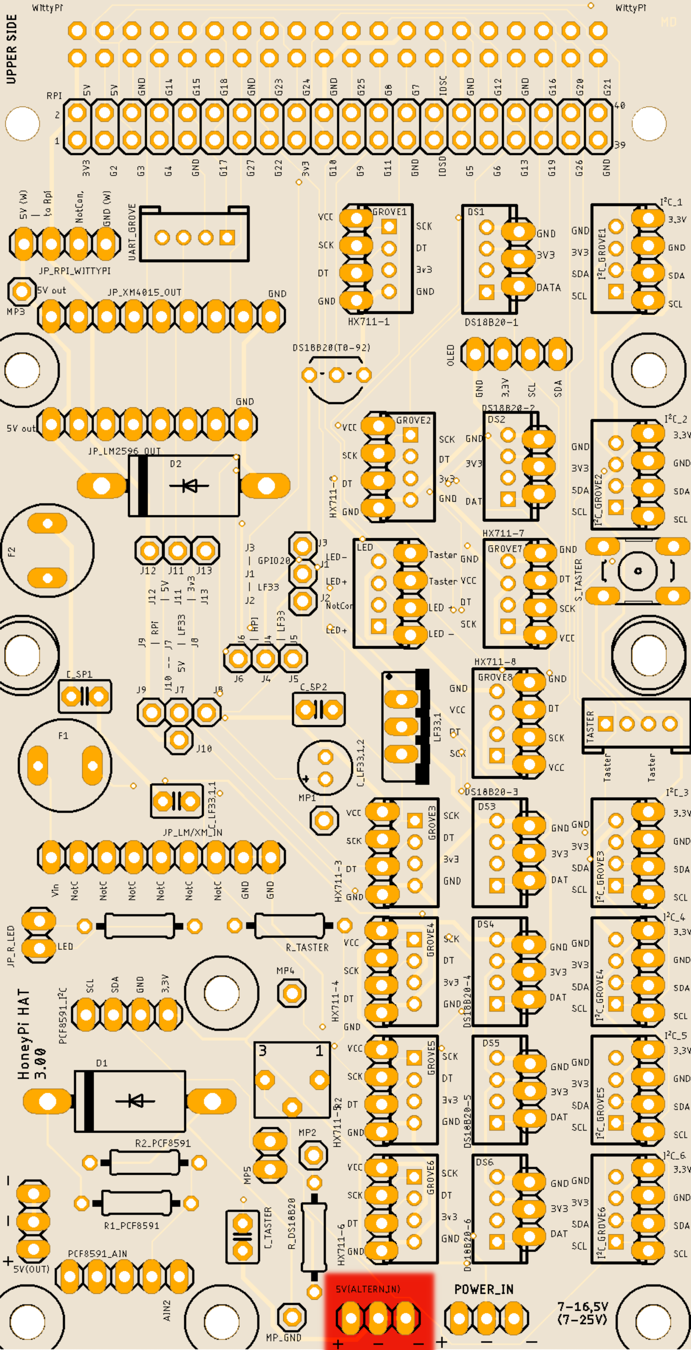
PCB_V3.x/Doku/PowerAlternativ.png
