Honey-Pi/honeypi-pcb/PCB_V3.x/Doku/PowerOhneWittyPi.png

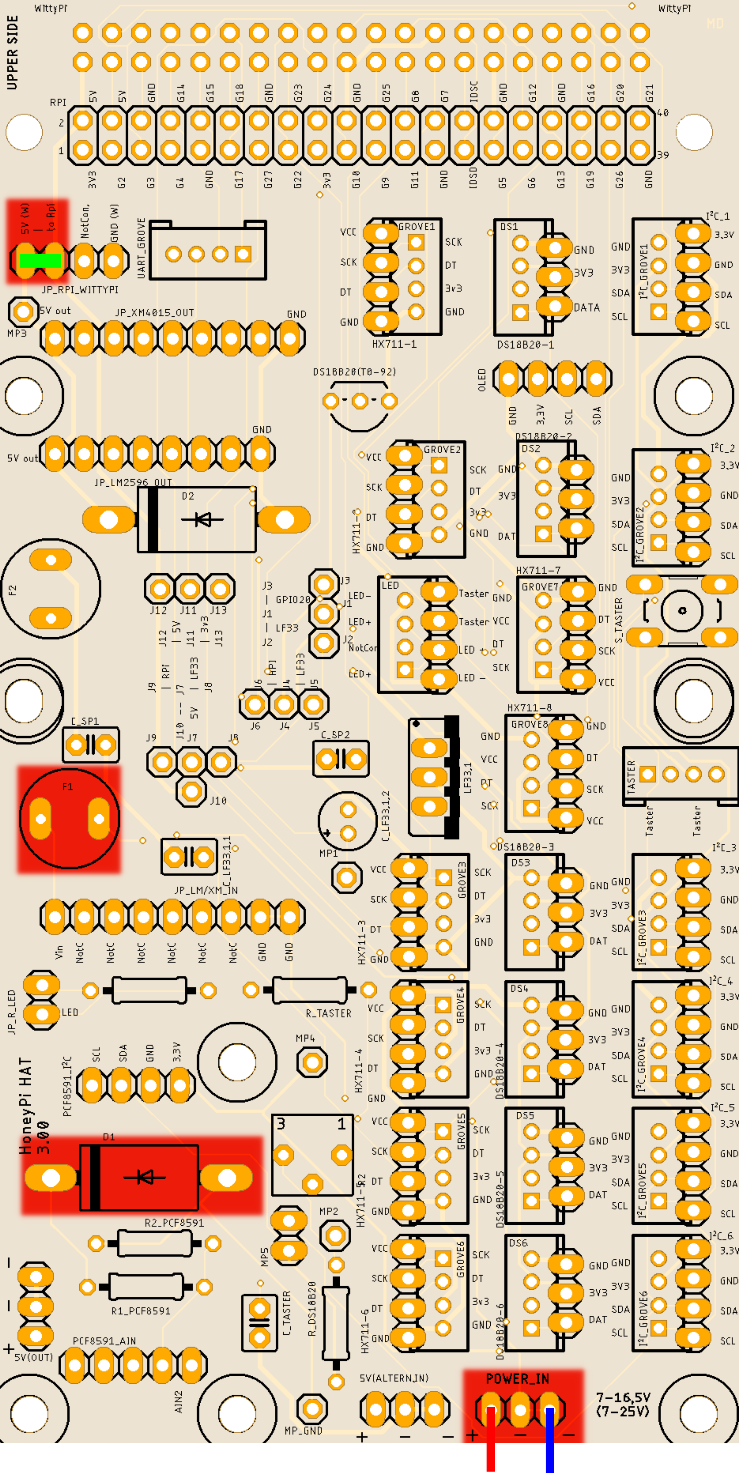
PCB_V3.x/Doku/PowerOhneWittyPi.png
