Honey-Pi/honeypi-pcb/PCB_V3.x/Doku/RPI_LF33.png

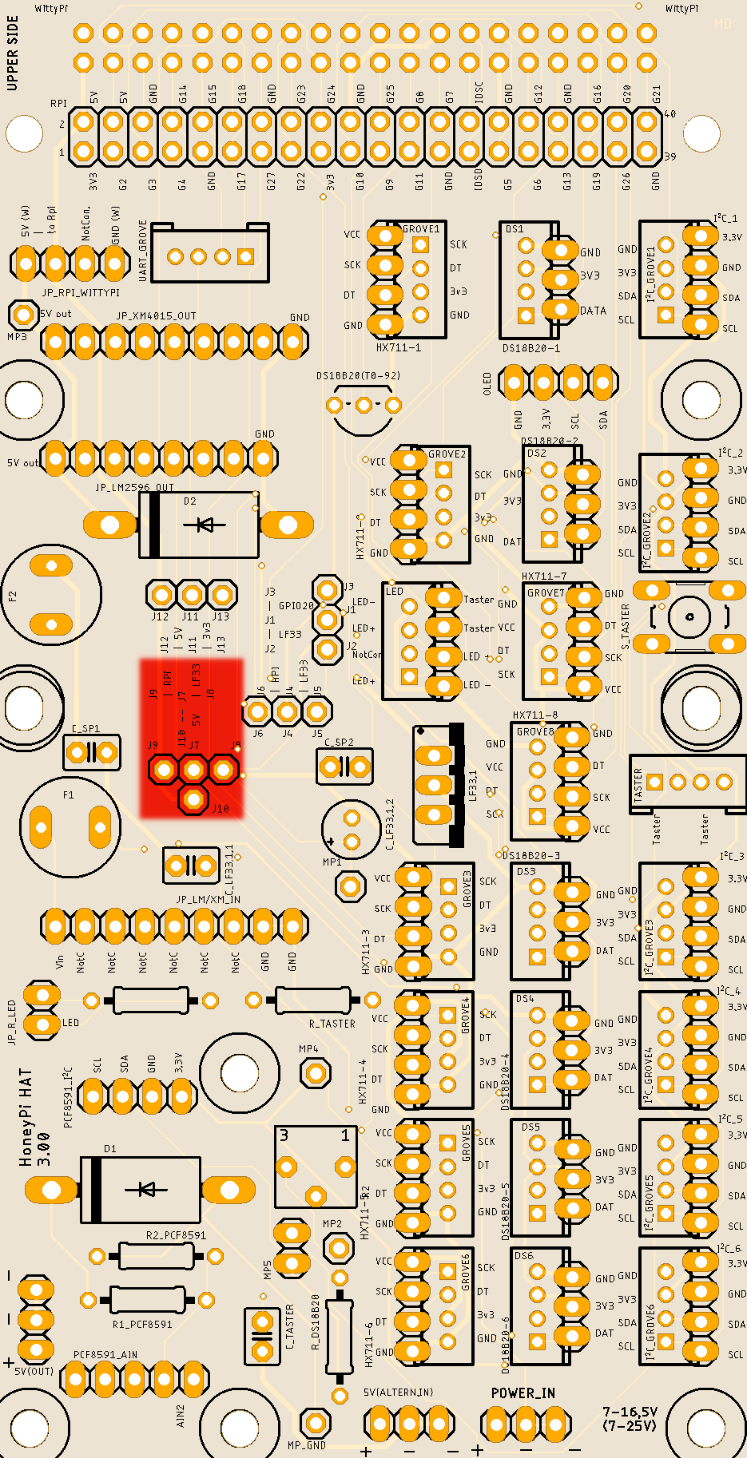
PCB_V3.x/Doku/RPI_LF33.png
