Honey-Pi/honeypi-pcb/PCB_V3.x/Doku/Taster.png

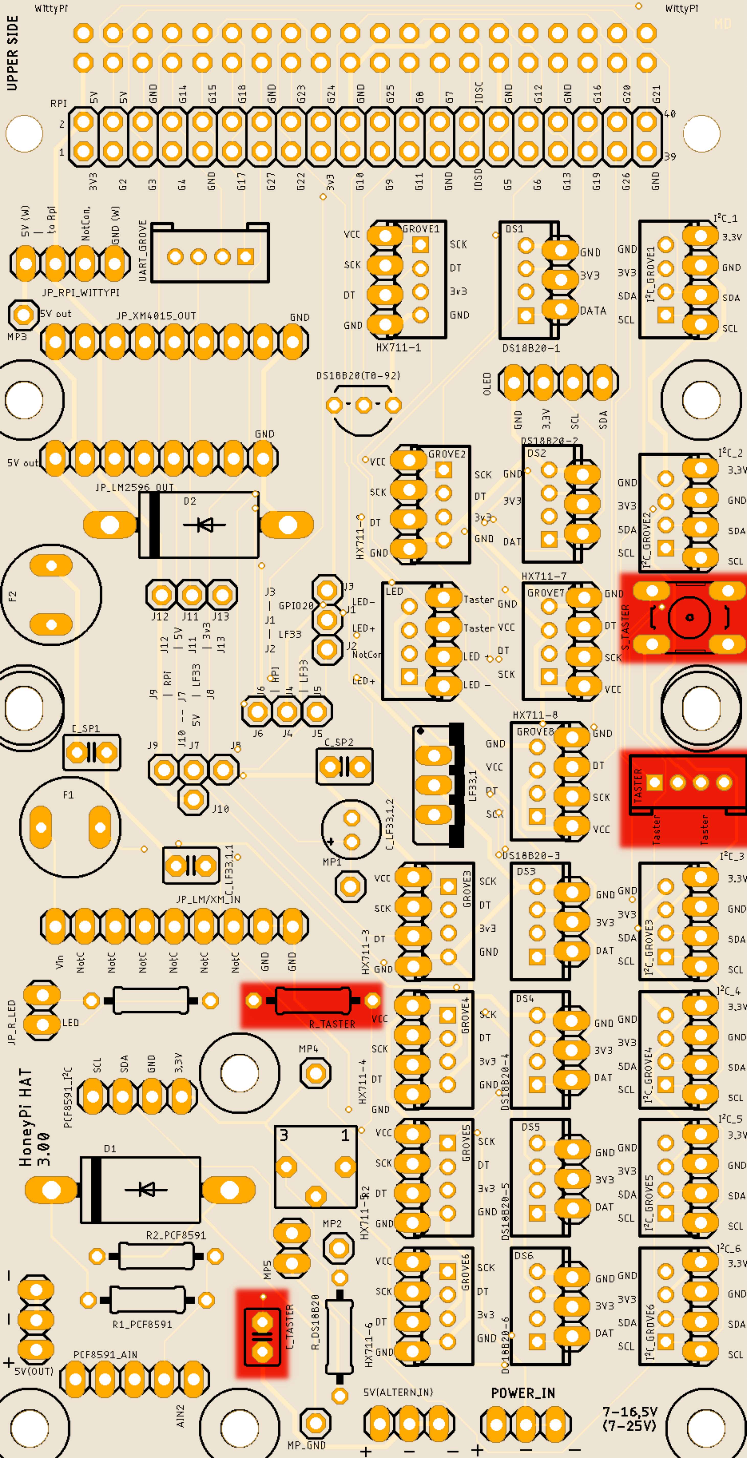
PCB_V3.x/Doku/Taster.png
