Honey-Pi/honeypi-pcb/PCB_V3.x/Doku/WittyCon.png

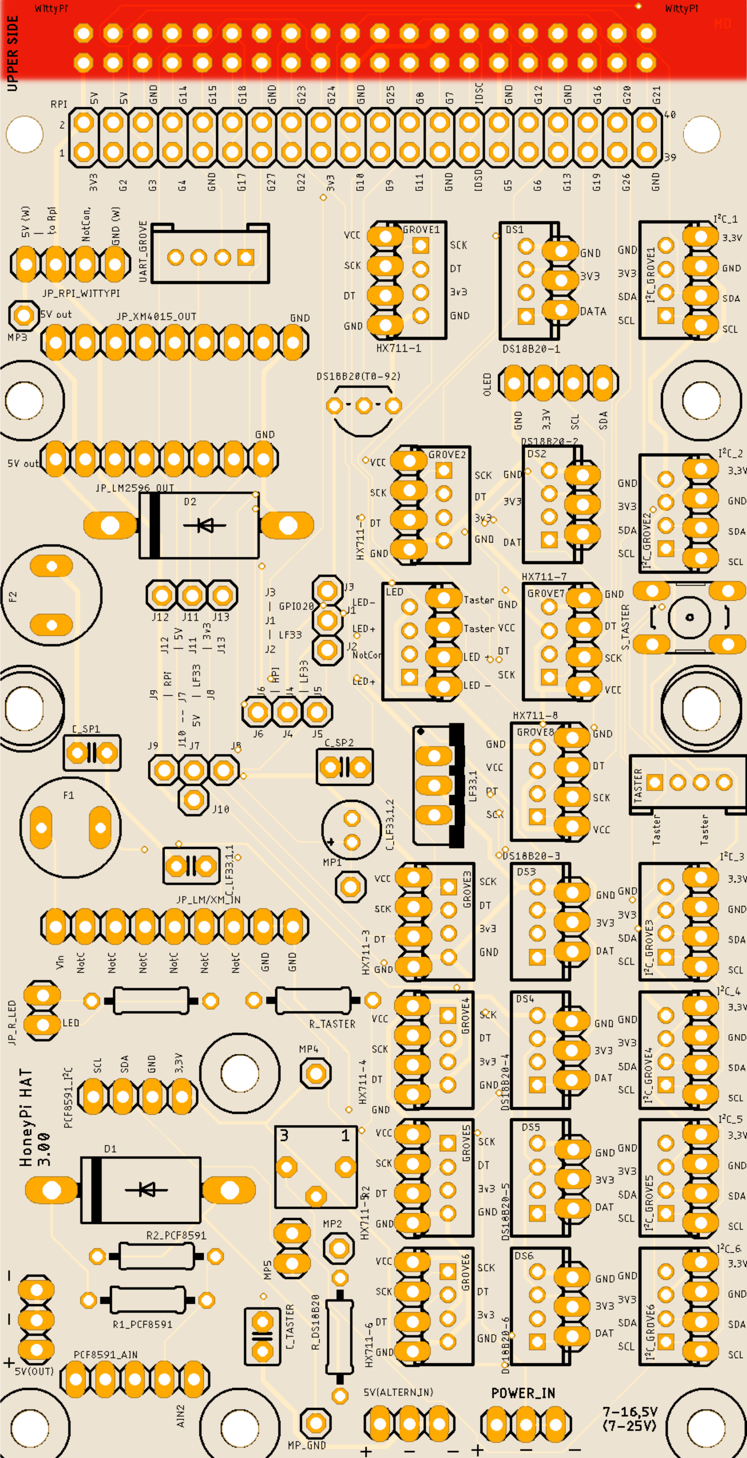
PCB_V3.x/Doku/WittyCon.png
