Honey-Pi/honeypi-pcb/PCB_V3.x/Pictures/V3.x_alpha_ Aufbau 3.jpg

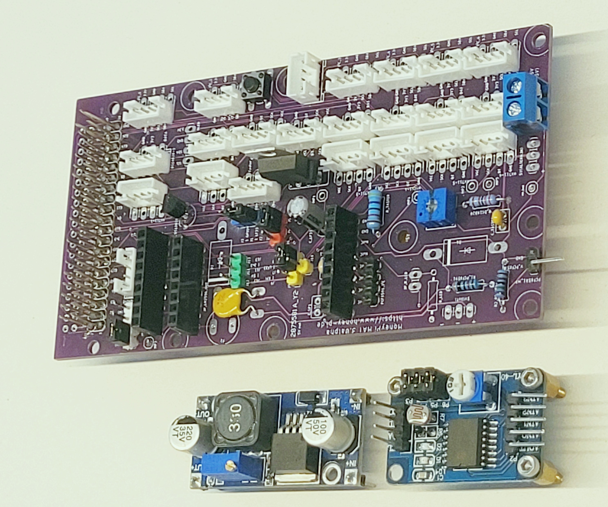
PCB_V3.x/Pictures/V3.x_alpha_ Aufbau 3.jpg
