Honey-Pi/honeypi-pcb/PCB_V2.x/HoneyPI_Platine 2.0.brd

## EAGLE design PCB_V2.x/HoneyPI_Platine 2.0.brd (2020-05-06, an earlier design)

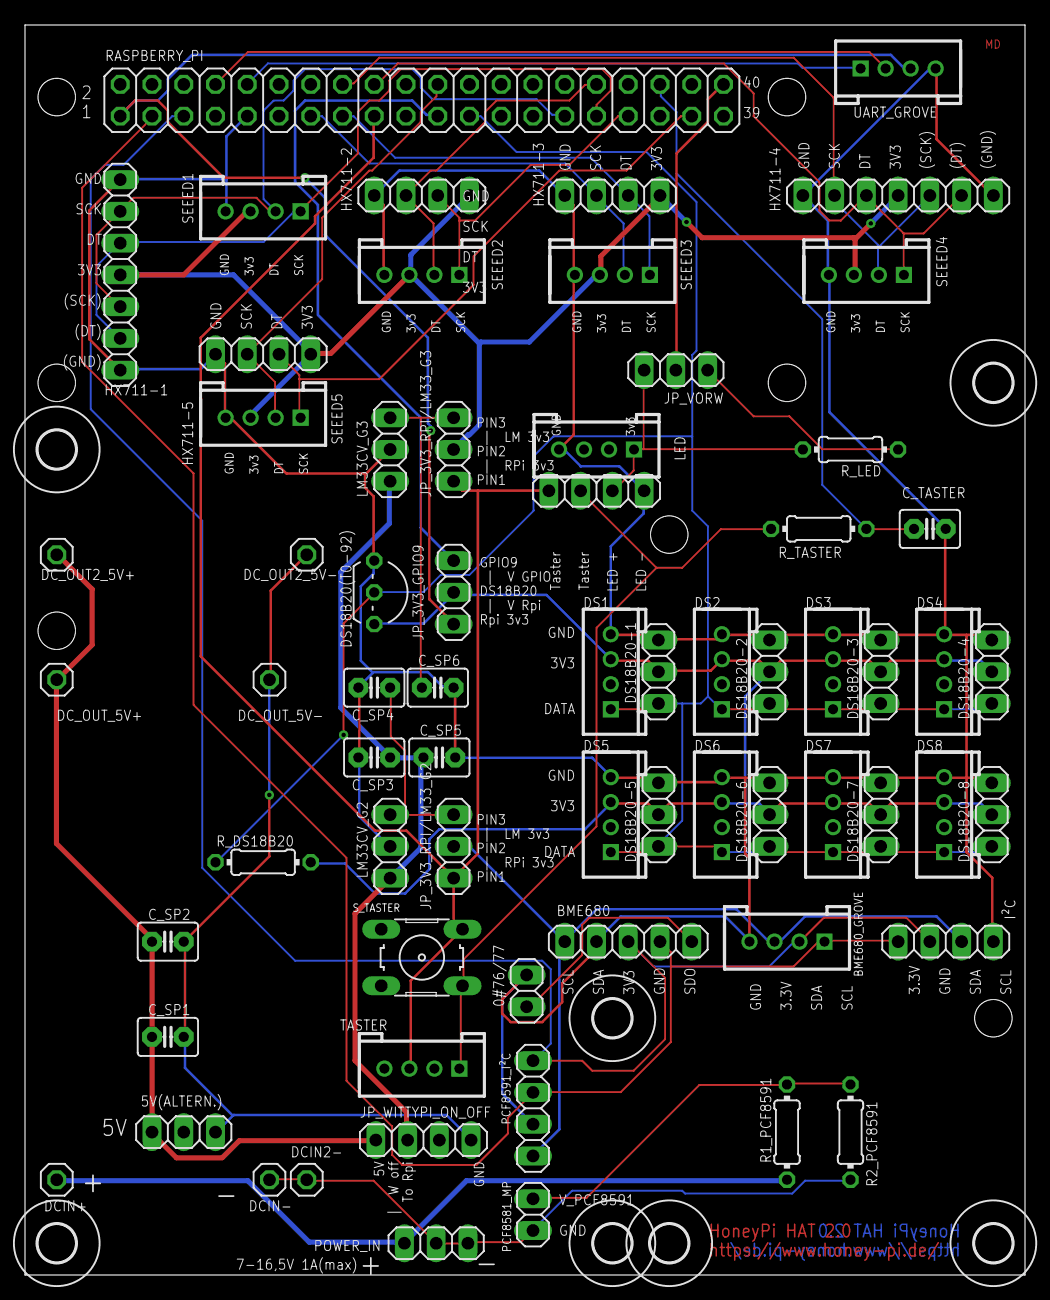
[picture p73: board HoneyPI_Platine 2.0.brd from above]

Board: 2 copper layers, 80.0 x 100.0 mm, 74 parts (0 on the bottom side), 36 nets.

Parts:
0#76/77: 1X02
5V(ALTERN.): 1X03
BME680: 1X05
BME680_GROVE: 4P-2.0
C_SP1, C_SP3, C_SP4, C_SP5, C_SP6: 100µF; C2.5-3
C_SP2: 1µF; C2.5-3
C_TASTER: 470nF; C2.5-3
DCIN2-: 1X01
DCIN+: 1X01
DCIN-: 1X01
DC_OUT2_5V+, DC_OUT2_5V-: 1X01
DC_OUT_5V+: 5V; 1X01
DC_OUT_5V-: GND; 1X01
DS1, DS2, DS3, DS4, DS5, DS6, DS7, DS8: 4P-2.0
DS18B20(T0-92): DS18b20; TO92-
DS18B20-1, DS18B20-2, DS18B20-3, DS18B20-4, DS18B20-5, DS18B20-6, DS18B20-7, DS18B20-8: 1X03
HX711-1, HX711-4: 1X07
HX711-2, HX711-3, HX711-5: 1X04
I²C: 1X04
JP_3V3_GPIO9, JP_3V3_RPI/LM33_G2, JP_3V3_RPI/LM33_G3: 1X03
JP_VORW: 1X03
JP_WITTYPI_ON_OFF: 1X04
LED: 4P-2.0
LM33CV_G2, LM33CV_G3: 1X03
PCF8581_MP: 1X02
PCF8591_I²C: 1X04
POWER_IN: 1X03
R1_PCF8591: 30K; 0204/7
R2_PCF8591: 7K5; 0204/7
RASPBERRY_PI: 2X20
R_DS18B20: 4K7; 0204/7
R_LED: 130; 0204/7
R_TASTER: 50K; 0204/7
SEEED1, SEEED2, SEEED3, SEEED4, SEEED5: 4P-2.0
S_TASTER: B3F-10XX
TASTER: 4P-2.0
TASTER_LED: 1X04
U$1, U$2, U$3, U$4, U$5, U$6, U$8: 3,0
UART_GROVE: 4P-2.0

Connections:
3V3: DS1.3, DS2.3, DS3.3, DS4.3, DS5.3, DS6.3, DS7.3, DS8.3, DS18B20(T0-92).3, DS18B20-1.2, DS18B20-2.2, DS18B20-3.2, DS18B20-4.2, DS18B20-5.2, DS18B20-6.2, DS18B20-7.2, DS18B20-8.2, JP_3V3_GPIO9.2, R_DS18B20.2
3V3_PIN1: JP_3V3_GPIO9.3, RASPBERRY_PI.1, UART_GROVE.3
3V3_PIN17: JP_3V3_RPI/LM33_G2.1, JP_3V3_RPI/LM33_G3.1, RASPBERRY_PI.17, S_TASTER.2, TASTER.3, TASTER_LED.1
5V_1: 5V(ALTERN.).1, C_SP1.1, C_SP2.1, DC_OUT2_5V+.1, DC_OUT_5V+.1, JP_WITTYPI_ON_OFF.1
5V_PIN2: C_SP3.1, C_SP5.1, JP_WITTYPI_ON_OFF.2, LM33CV_G2.1, LM33CV_G3.1
BME_SCL/SCK_PIN5: BME680.3, BME680_GROVE.2, I²C.2, PCF8591_I²C.4, RASPBERRY_PI.5
BME_SDI/SDA_PIN3: BME680.4, BME680_GROVE.1, I²C.1, PCF8591_I²C.3, RASPBERRY_PI.3
DS18B20_3V3_GPIO9_PIN21: JP_3V3_GPIO9.1, RASPBERRY_PI.21
DS18B20_DATA_GPIO11_PIN23: DS1.1, DS2.1, DS3.1, DS4.1, DS5.1, DS6.1, DS7.1, DS8.1, DS18B20(T0-92).2, DS18B20-1.1, DS18B20-2.1, DS18B20-3.1, DS18B20-4.1, DS18B20-5.1, DS18B20-6.1, DS18B20-7.1, DS18B20-8.1, RASPBERRY_PI.23, R_DS18B20.1
GND: 5V(ALTERN.).3, C_SP1.2, C_SP2.2, DC_OUT2_5V-.1, DC_OUT_5V-.1, JP_WITTYPI_ON_OFF.4
GND_2: 0#76/77.1, BME680.2, BME680_GROVE.4, C_SP3.2, C_SP4.2, C_SP5.2, C_SP6.2, C_TASTER.1, DS1.4, DS2.4, DS3.4, DS4.4, DS5.4, DS6.4, DS7.4, DS8.4, DS18B20(T0-92).1, DS18B20-1.3, DS18B20-2.3, DS18B20-3.3, DS18B20-4.3, DS18B20-5.3, DS18B20-6.3, DS18B20-7.3, DS18B20-8.3, HX711-1.1, HX711-1.7, HX711-2.1, HX711-3.1, HX711-4.1, HX711-4.7, HX711-5.1, I²C.4, LED.4, LM33CV_G2.2, LM33CV_G3.2, PCF8591_I²C.2, RASPBERRY_PI.9, SEEED1.4, SEEED2.4, SEEED3.4, SEEED4.4, SEEED5.4, TASTER_LED.4, UART_GROVE.4
HX711(5)-SCK_GPIO26_PIN37: HX711-5.3, RASPBERRY_PI.37, SEEED5.1
HX711-DT_GPIO5_PIN29: HX711-1.2, HX711-1.5, RASPBERRY_PI.29, SEEED1.2
HX711-DT_GPIO23_PIN16: HX711-4.2, HX711-4.5, RASPBERRY_PI.16, SEEED4.2
HX711-DT_GPIO25_PIN22: HX711-5.2, RASPBERRY_PI.22, SEEED5.2
HX711-DT_RPI-GPIO12_PIN32: HX711-2.2, RASPBERRY_PI.32, SEEED2.2
HX711-DT_RPI-GPIO27_PIN13: HX711-3.2, RASPBERRY_PI.13, SEEED3.2
HX711-SCK_GPIO6_PIN31: HX711-1.3, HX711-1.6, RASPBERRY_PI.31, SEEED1.1
HX711-SCK_GPIO24_PIN18: HX711-4.3, HX711-4.6, RASPBERRY_PI.18, SEEED4.1
HX711-SCK_RPI-GPIO13_PIN33: HX711-2.3, RASPBERRY_PI.33, SEEED2.1
HX711-SCK_RPI-GPIO22_PIN15: HX711-3.3, RASPBERRY_PI.15, SEEED3.1
HX711_V: HX711-1.4, HX711-2.4, HX711-3.4, HX711-4.4, HX711-5.4, JP_3V3_RPI/LM33_G3.2, SEEED1.3, SEEED2.3, SEEED3.3, SEEED4.3, SEEED5.3
I²C_V: BME680.1, BME680_GROVE.3, I²C.3, JP_3V3_RPI/LM33_G2.2, PCF8591_I²C.1
LED_2: JP_VORW.3, LED.1, R_LED.2, TASTER_LED.3
LED_GPIO21_PIN40: JP_VORW.2, RASPBERRY_PI.40
unnamed: DCIN2-.1, DCIN-.1, PCF8581_MP.2, POWER_IN.2, POWER_IN.3, R2_PCF8591.2
unnamed: C_SP4.1, JP_3V3_RPI/LM33_G2.3, LM33CV_G2.3
unnamed: R_TASTER.1, S_TASTER.4, TASTER.1, TASTER_LED.2
unnamed: C_SP6.1, JP_3V3_RPI/LM33_G3.3, LM33CV_G3.3
unnamed: PCF8581_MP.1, R1_PCF8591.2, R2_PCF8591.1
unnamed: 0#76/77.2, BME680.5
unnamed: JP_VORW.1, R_LED.1
unnamed: DCIN+.1, POWER_IN.1, R1_PCF8591.1
RX_0_PIN_10: RASPBERRY_PI.10, UART_GROVE.1
TASTER_GPIO16_PIN36: C_TASTER.2, RASPBERRY_PI.36, R_TASTER.2
TX_0_PIN_8: RASPBERRY_PI.8, UART_GROVE.2
